mkygogo/trlc-dk1/hardware/leader_parts/link5-6-1_v0.1.0.stl

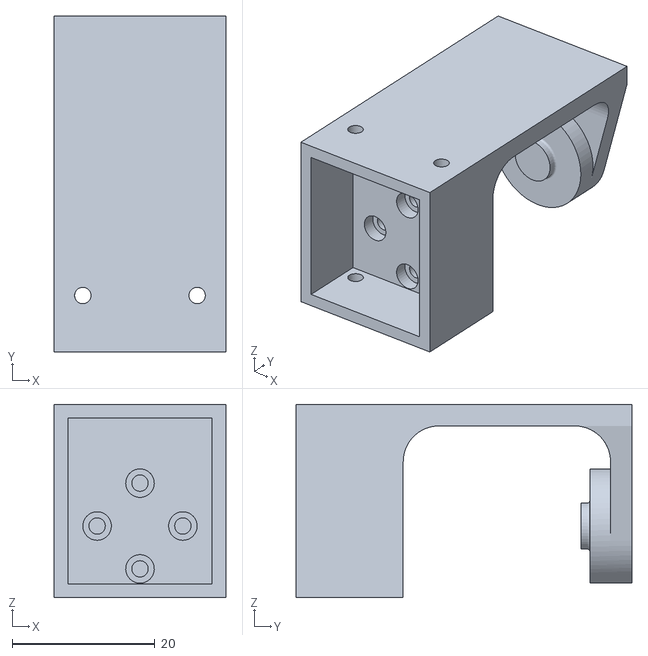
[picture p19: CAD file, 2025-09-08]
hardware/leader_parts/link5-6-1_v0.1.0.stl
24.0 x 47.0 x 27.0
