mkygogo/trlc-dk1/hardware/follower_parts/gripper/uvc-camera-mount_v0.1.0.step

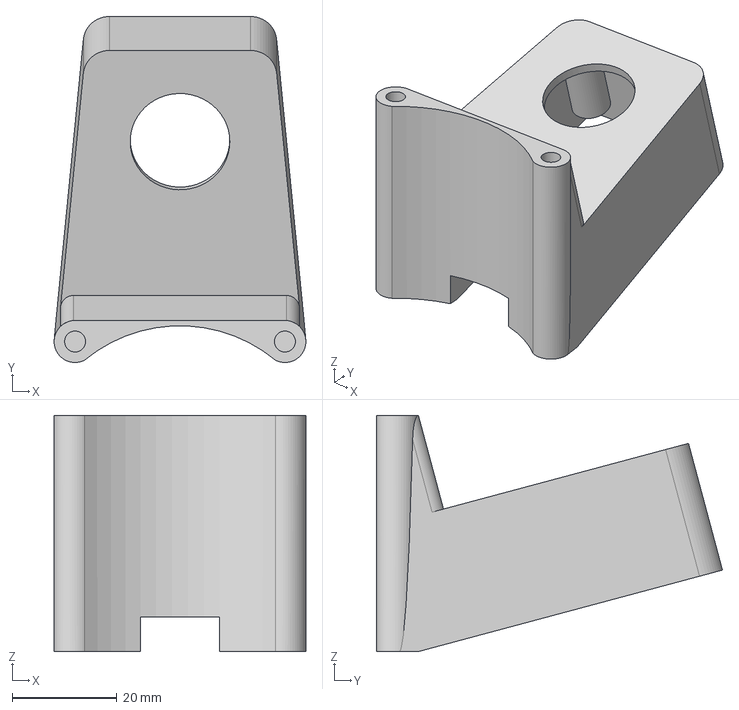
[picture p20: CAD file, 2025-09-23]
hardware/follower_parts/gripper/uvc-camera-mount_v0.1.0.step
48.0 x 66.0 x 45.0 mm
