mkygogo/trlc-dk1/hardware/follower_parts/link3-4-1_v0.1.0.step

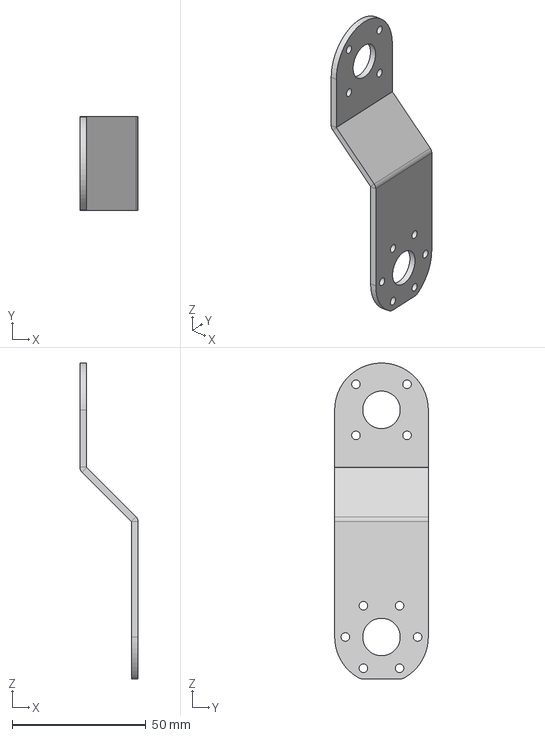
[picture p21: CAD file, 2025-09-23]
hardware/follower_parts/link3-4-1_v0.1.0.step
21.8 x 35.0 x 118.0 mm
