mkygogo/trlc-dk1/hardware/leader_parts/link3-4_v0.1.0.stl

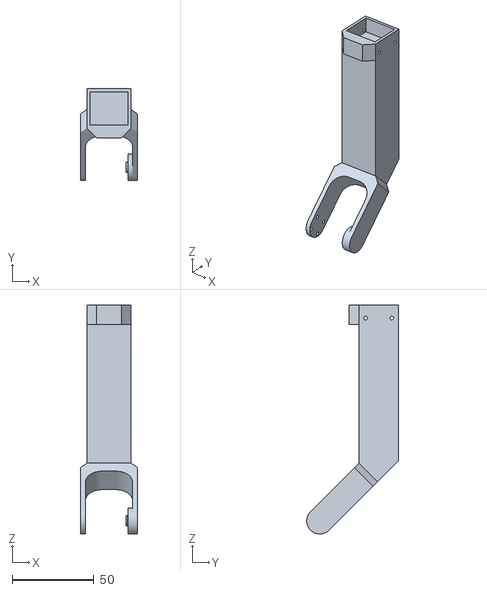
[picture p22: CAD file, 2025-09-08]
hardware/leader_parts/link3-4_v0.1.0.stl
35.0 x 56.0 x 139.9
