mkygogo/trlc-dk1/hardware/follower_parts/gripper/link6-7-1_v0.1.0.step

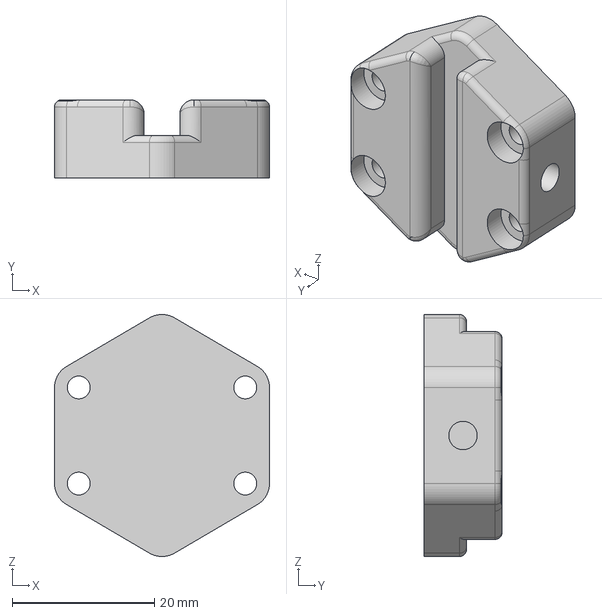
[picture p23: CAD file, 2025-09-23]
hardware/follower_parts/gripper/link6-7-1_v0.1.0.step
30.2 x 11.0 x 34.0 mm
