mkygogo/trlc-dk1/hardware/follower_parts/link1-2-rest_v0.1.0.step

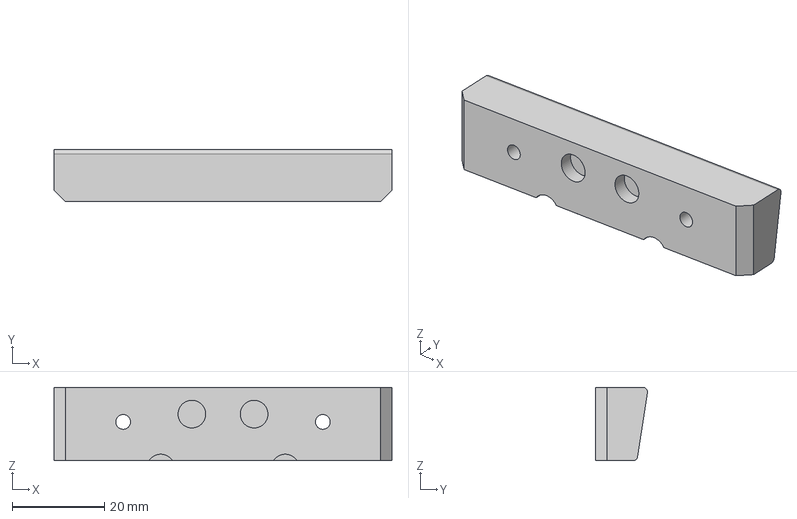
[picture p24: CAD file, 2025-09-23]
hardware/follower_parts/link1-2-rest_v0.1.0.step
73.3 x 11.3 x 15.9 mm
