mkygogo/trlc-dk1/hardware/leader_parts/link2-3_v0.1.0.stl

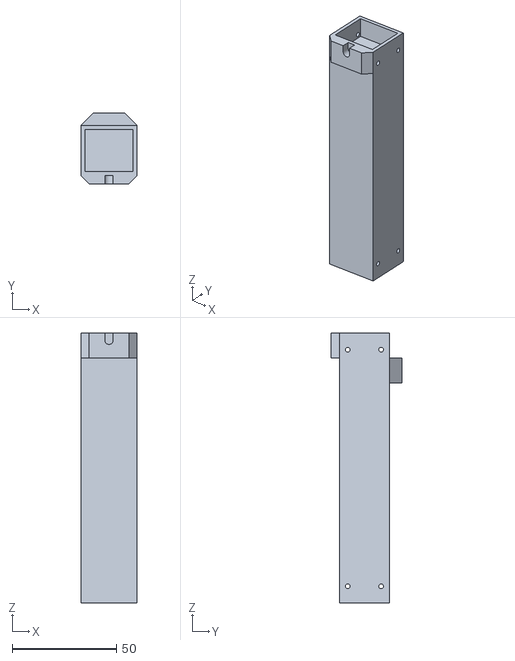
[picture p25: CAD file, 2025-09-08]
hardware/leader_parts/link2-3_v0.1.0.stl
27.0 x 34.0 x 129.5
