mkygogo/trlc-dk1/hardware/follower_parts/dm-adapter_v0.1.0.step

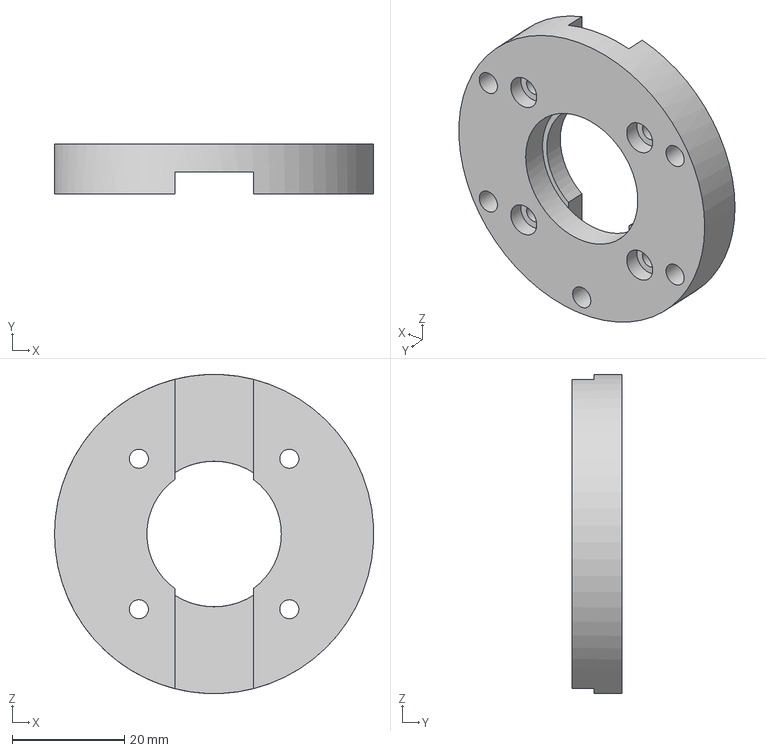
[picture p26: CAD file, 2025-09-23]
hardware/follower_parts/dm-adapter_v0.1.0.step
57.0 x 9.00 x 57.0 mm
