mkygogo/trlc-dk1/hardware/follower_parts/gripper/link6-7-2_v0.1.0.step

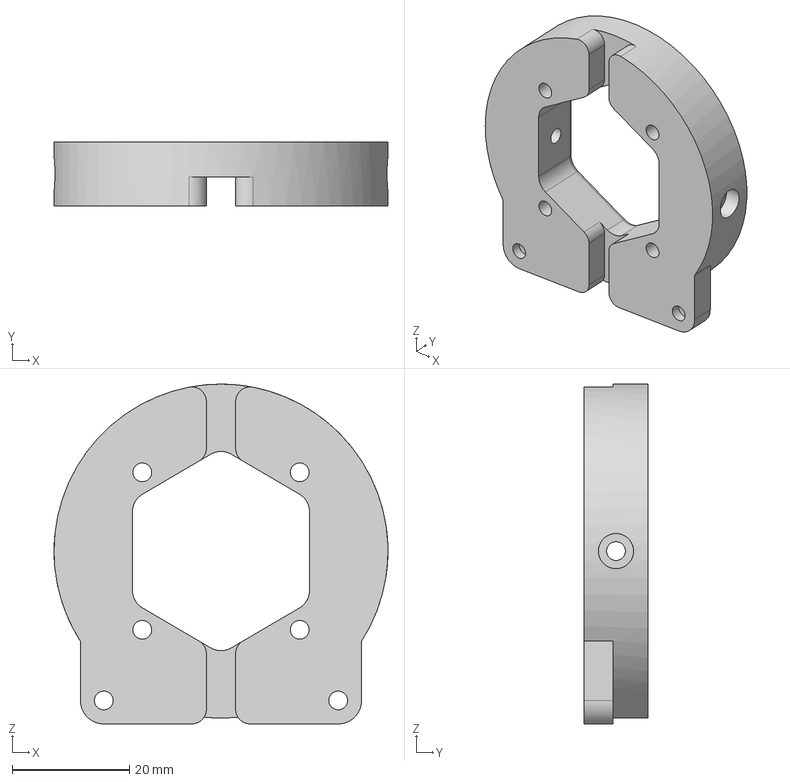
[picture p27: CAD file, 2025-09-23]
hardware/follower_parts/gripper/link6-7-2_v0.1.0.step
57.0 x 11.0 x 58.0 mm
