mkygogo/trlc-dk1/hardware/leader_parts/gello_trigger.STL

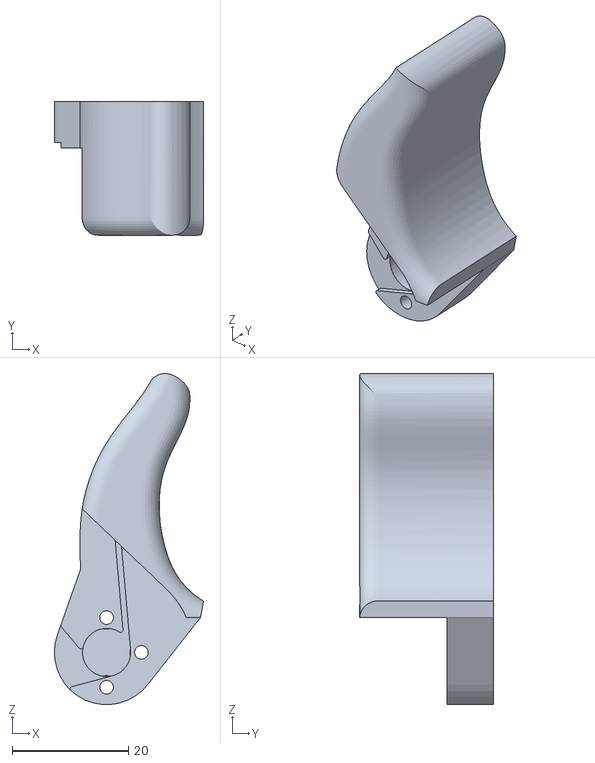
[picture p28: CAD file, 2025-09-08]
hardware/leader_parts/gello_trigger.STL
25.7 x 23.0 x 57.0
