mkygogo/trlc-dk1/hardware/follower_parts/dm-shaft-extension_v0.1.0.step

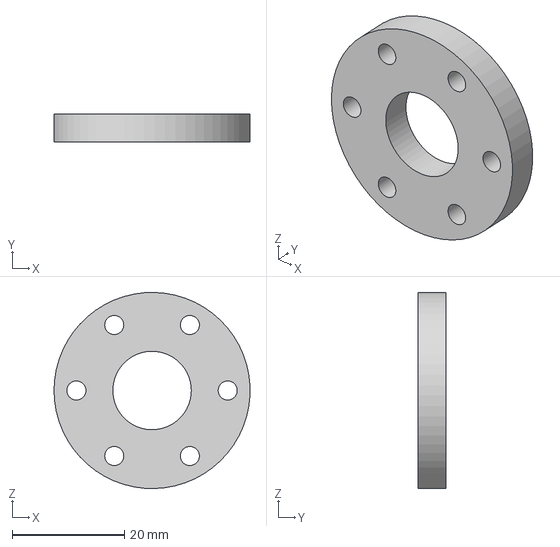
[picture p29: CAD file, 2025-09-23]
hardware/follower_parts/dm-shaft-extension_v0.1.0.step
35.0 x 5.00 x 35.0 mm
