mkygogo/trlc-dk1/hardware/follower_parts/gripper/d405-camera-mount_v0.1.0.step

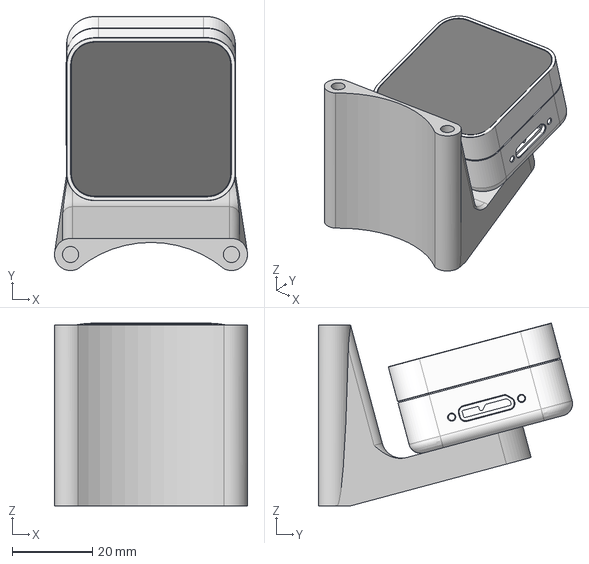
[picture p30: CAD file, 2025-09-23]
hardware/follower_parts/gripper/d405-camera-mount_v0.1.0.step
48.0 x 63.2 x 45.5 mm
D405_Solid
DIN 912 - M3 x 0.5 x 10 Steel 4.6 Plain x 2
