mkygogo/trlc-dk1/hardware/leader_parts/gello_handle.STL

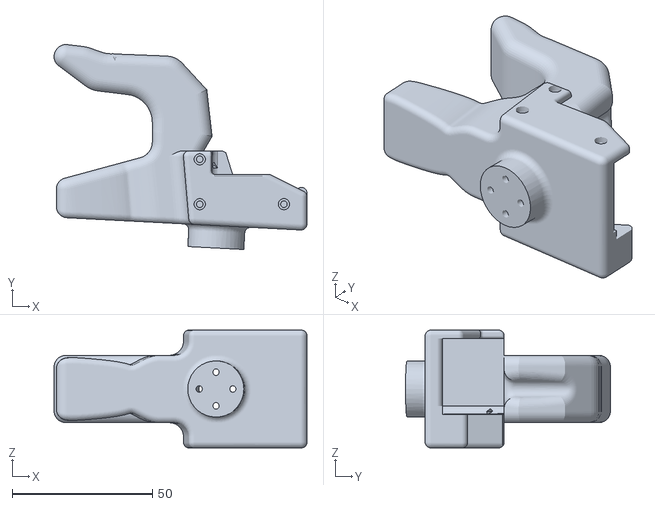
[picture p31: CAD file, 2025-09-08]
hardware/leader_parts/gello_handle.STL
90.2 x 73.1 x 42.0
