mkygogo/trlc-dk1/hardware/follower_parts/link3-4-1-adjusted_v0.1.0.step

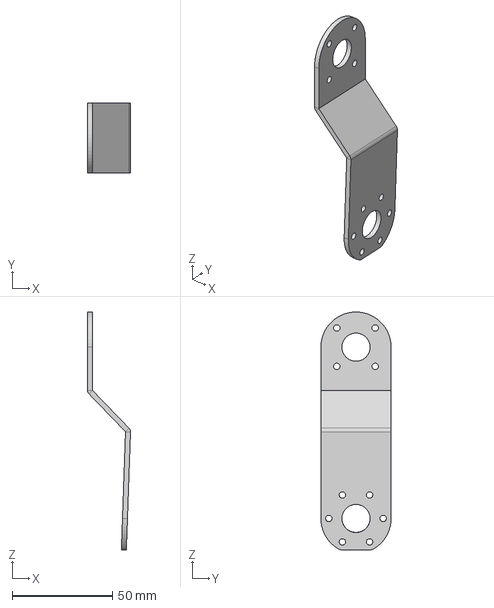
[picture p32: CAD file, 2025-09-23]
hardware/follower_parts/link3-4-1-adjusted_v0.1.0.step
21.4 x 35.0 x 118.4 mm
