mkygogo/trlc-dk1/hardware/follower_parts/link3-4-2_v0.1.0.step

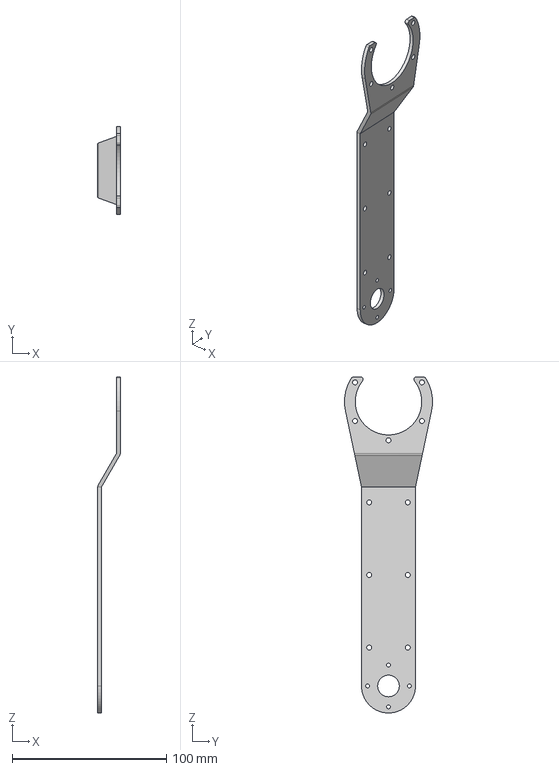
[picture p33: CAD file, 2025-09-23]
hardware/follower_parts/link3-4-2_v0.1.0.step
14.6 x 57.0 x 217.5 mm
