mkygogo/trlc-dk1/hardware/leader_parts/link1-2_v0.1.0.stl

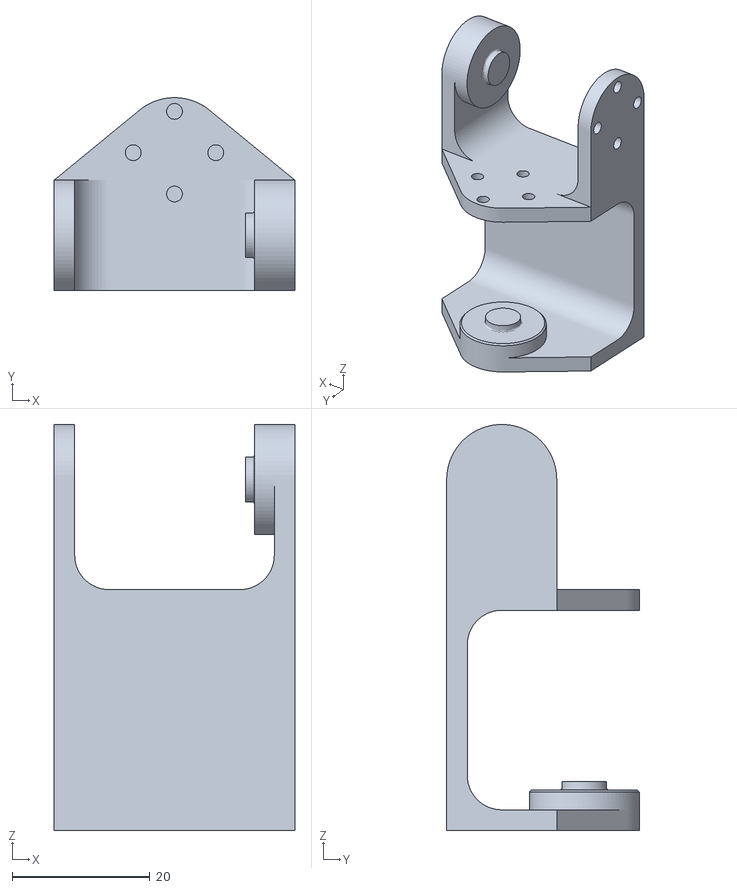
[picture p34: CAD file, 2025-09-08]
hardware/leader_parts/link1-2_v0.1.0.stl
35.0 x 28.0 x 59.0
