mkygogo/trlc-dk1/hardware/follower_parts/link0-1_v0.1.0.step

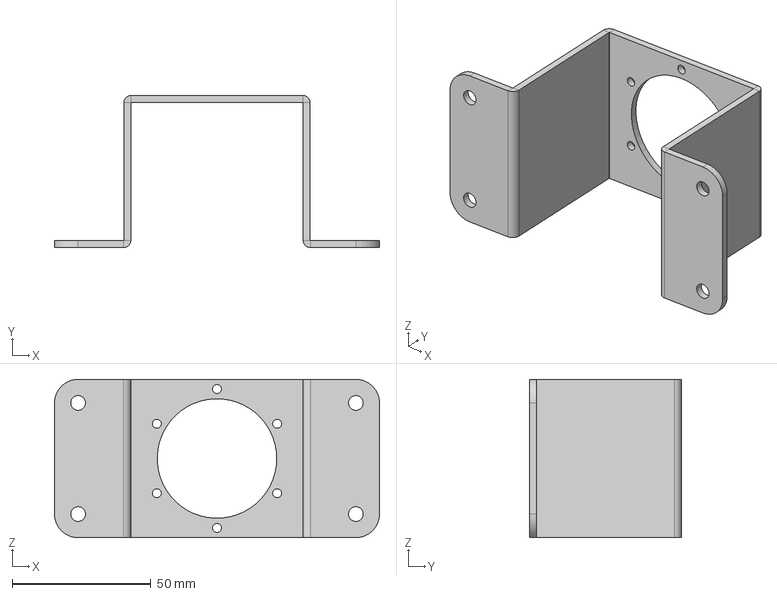
[picture p35: CAD file, 2025-09-23]
hardware/follower_parts/link0-1_v0.1.0.step
117.0 x 54.8 x 57.0 mm
