mkygogo/trlc-dk1/hardware/leader_parts/link5-6-2_v0.1.0.stl

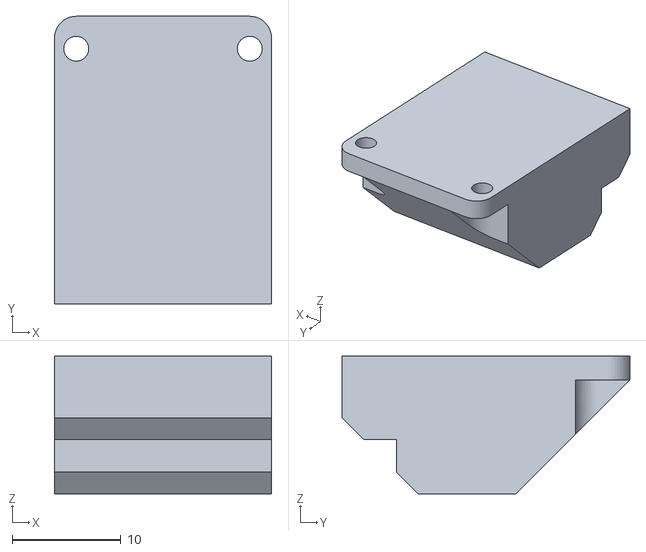
[picture p36: CAD file, 2025-09-08]
hardware/leader_parts/link5-6-2_v0.1.0.stl
20.0 x 26.5 x 12.7
