mkygogo/trlc-dk1/hardware/follower_parts/link2-3_v0.1.0.step

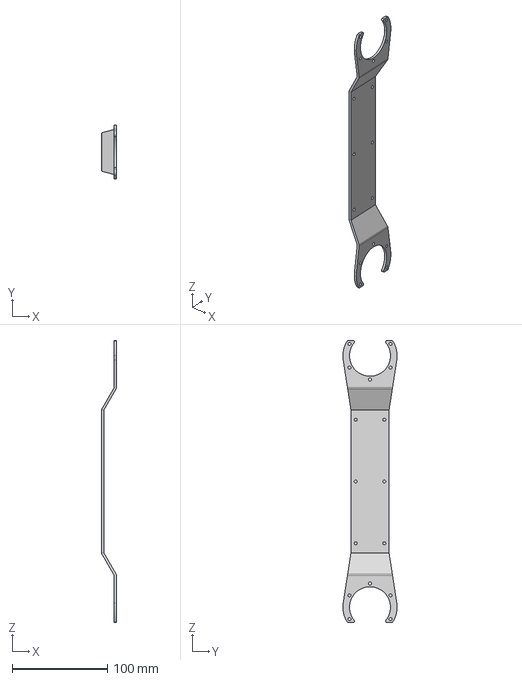
[picture p37: CAD file, 2025-09-23]
hardware/follower_parts/link2-3_v0.1.0.step
15.8 x 57.0 x 296.0 mm
