mkygogo/trlc-dk1/hardware/follower_parts/link5-6-rest_v0.1.0.step

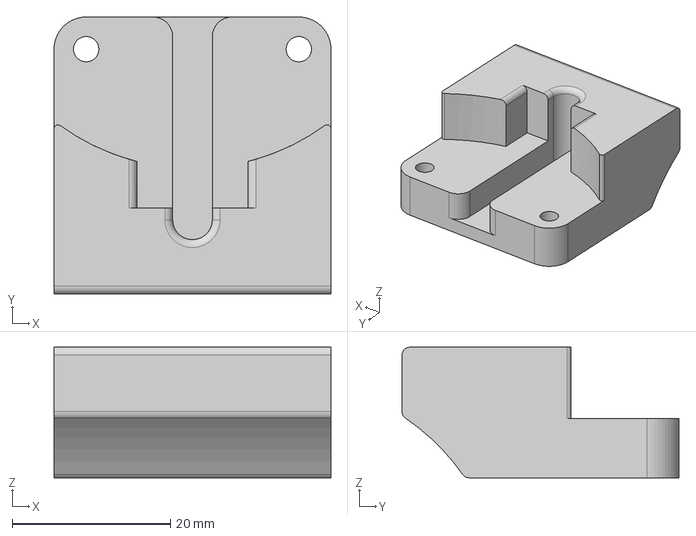
[picture p38: CAD file, 2025-09-23]
hardware/follower_parts/link5-6-rest_v0.1.0.step
35.0 x 35.0 x 16.5 mm
