mkygogo/trlc-dk1/hardware/follower_parts/link1-2_v0.1.0.step

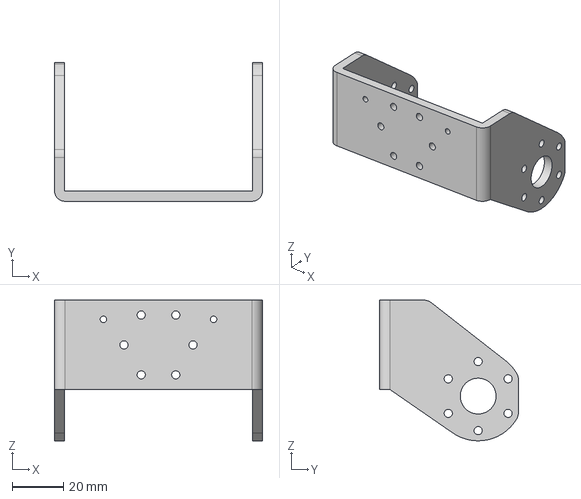
[picture p39: CAD file, 2025-09-23]
hardware/follower_parts/link1-2_v0.1.0.step
81.3 x 54.2 x 55.0 mm
